hejoin/STLinkV2/3DMODEL/Исходники/assembly.SLDASM

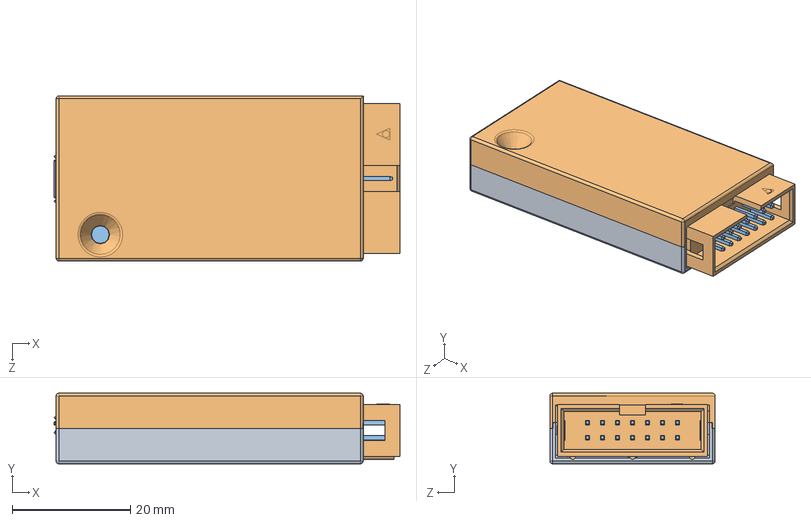
[picture p2: CAD file, 2015-11-19]
3DMODEL/Исходники/assembly.SLDASM
58.6 x 12.0 x 28.0 mm
bottom
top
Board
sod_123_body x 2
sod_123_pin x 4
C0603R x 22
C0603C x 9
CAPMP3216X180N
User_Library-IDC-14MS_Case_IDC-14MS
User_Library-IDC-14MS_Pin_1 x 14
SOT23-5 x 2
SW3dPS-SOT-223-1
User_Library-Quad50M48
HC-49
Extruded
Extruded_2
Extruded_3
Extruded_4
