hejoin/STLinkV2/3DMODEL/Для печати/bottom.STL

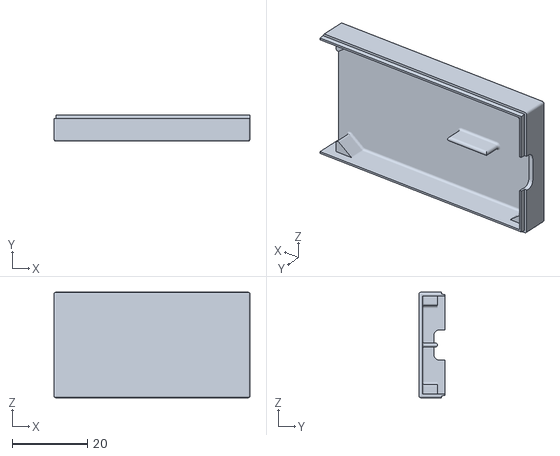
[picture p3: CAD file, 2015-11-19]
3DMODEL/Для печати/bottom.STL
52.0 x 7.00 x 28.0
