hejoin/STLinkV2/3DMODEL/Для печати/top.STL

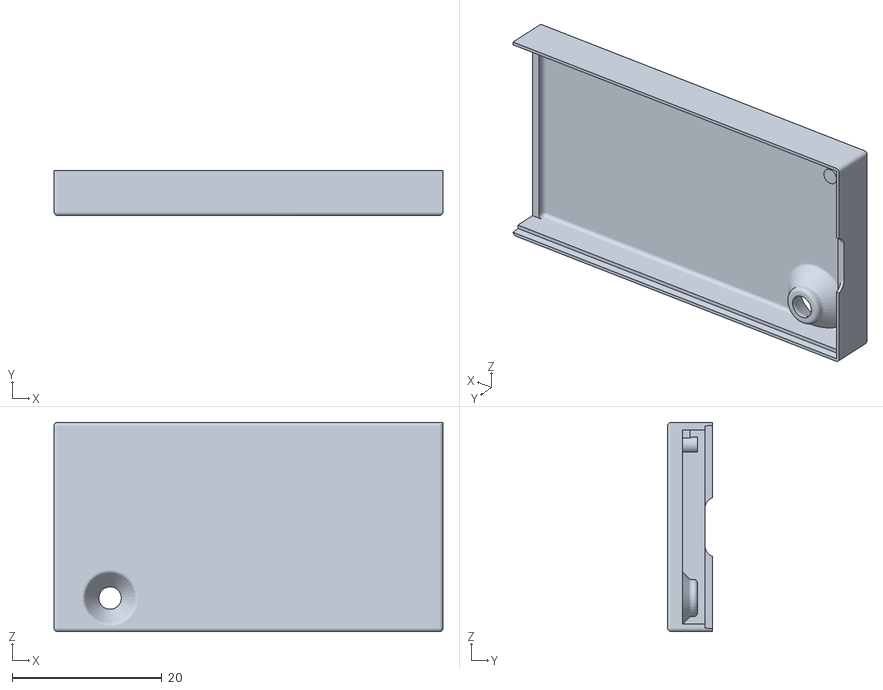
[picture p4: CAD file, 2015-11-19]
3DMODEL/Для печати/top.STL
52.0 x 6.00 x 28.0
